ThomasDuvinage/UTBM_TZ20/hardware/electronic/electronic_schematic.sch

## EAGLE design hardware/electronic/electronic_schematic.sch (2020-06-02)

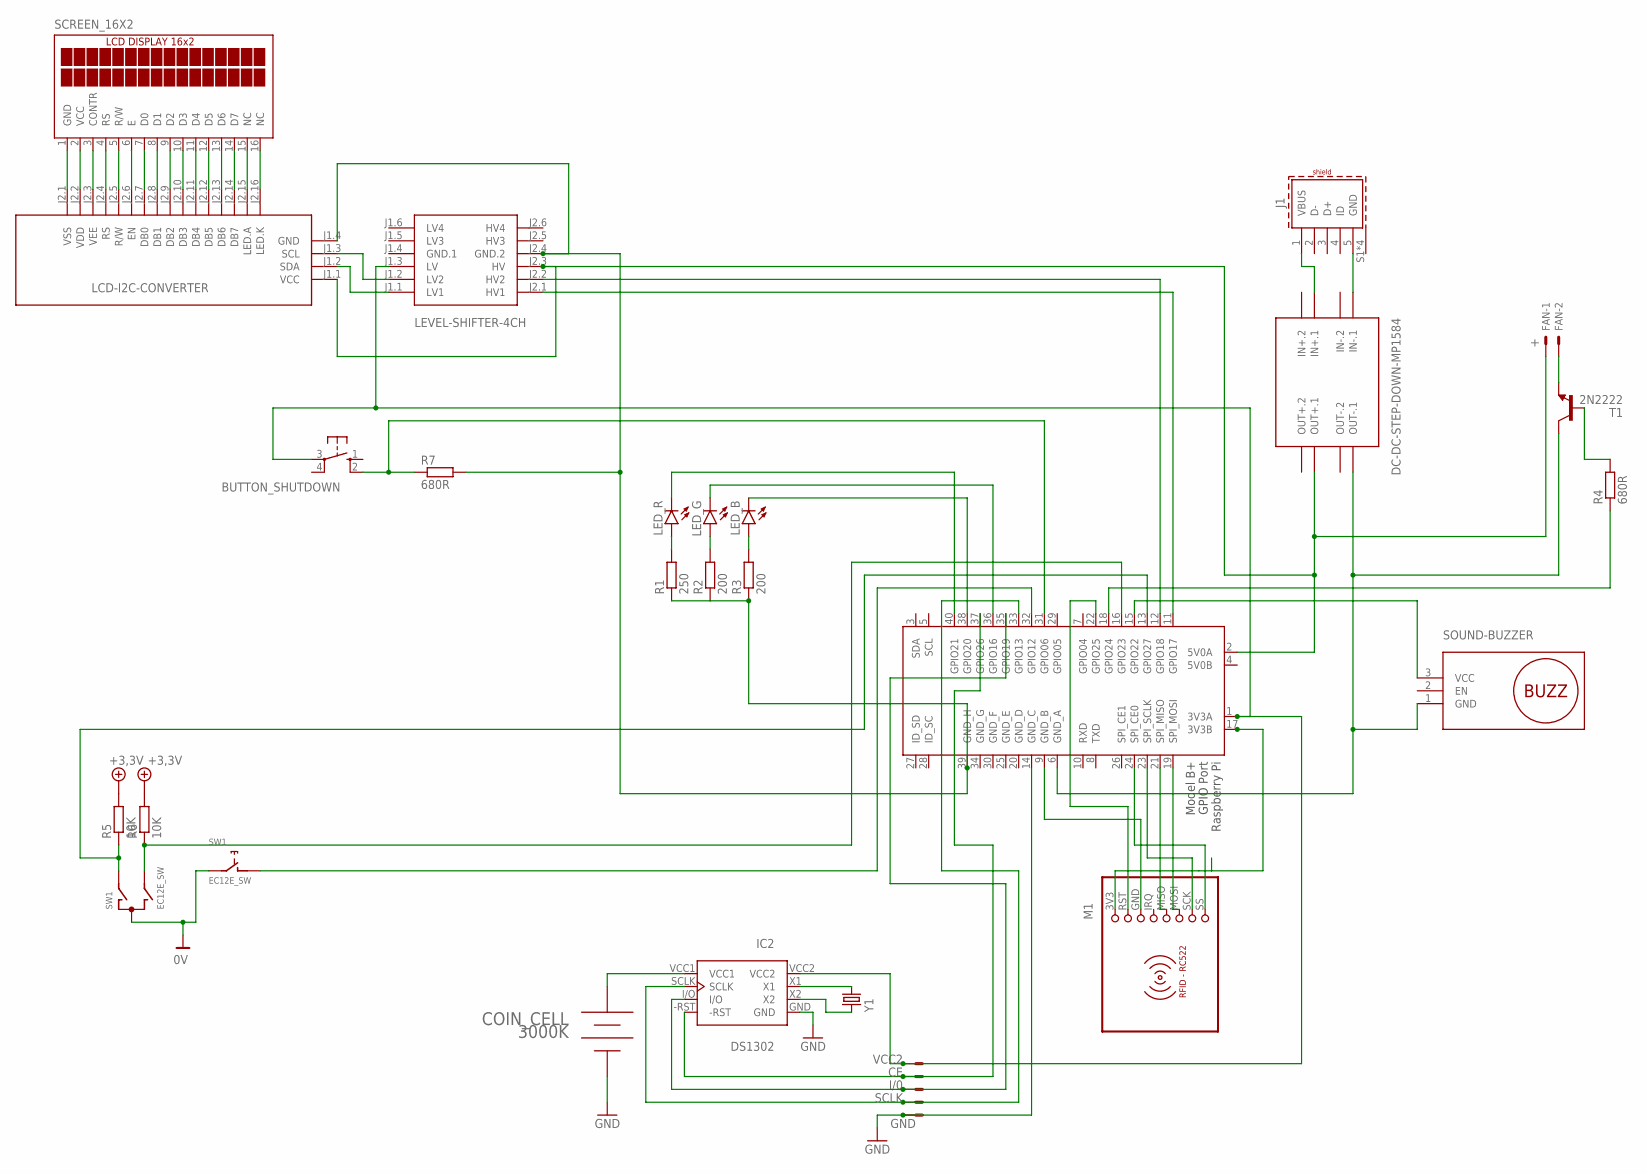
[picture p30: schematic electronic_schematic.sch]

Parts:
BUTTON_SHUTDOWN: 10-XX; B3F-10XX
COIN_CELL: 3000K
FAN: +; 22-23-2021
IC2: DS1302; DIL08
J1: 629105136821
LED_B: LED3MM
LED_G: LED3MM
LED_R: LED3MM
M1: RFID-RC522
R1: 250; 0207/10
R2, R3: 200; 0207/10
R4, R7: 680R; 0207/10
R5, R6: 10K; 0207/10
RTC: 22-23-2051
SCREEN_16X2: TUXGR_16X2_R2
SW1: EC12E_SW; ALPS_EC12E_SW
T1: 2N2222; TO18
U$1: LCD-I2C-CONVERTER
U$2: LEVEL-SHIFTER-4CH
U$4: SOUND-BUZZER
U$5: DC-DC-STEP-DOWN-MP1584
X1: RASPI_GPIO_B+#_BOX; RASPI_GPIO_B+_BOX
Y1: CC1V

Connections:
5+: FAN.1, U$1.J1.1 (VCC), U$2.J2.3 (HV), U$5.OUT+.1, X1.2 (5V0A)
+5V: R5.2, R6.2
-: COIN_CELL.-
CE: IC2.-RST, RTC.4, X1.37 (GPIO26)
GND: IC2.GND, RTC.1, SW1.C, SW1.E (2), X1.14 (GND_C)
I/0: IC2.I/O, RTC.3, X1.35 (GPIO19)
unnamed: LED_R.A, R1.2
unnamed: LED_G.A, R2.2
unnamed: LED_B.A, R3.2
unnamed: J1.5 (GND), U$5.IN-.1
unnamed: J1.1 (VBUS), U$5.IN+.1
unnamed: M1.SS (8), X1.24 (SPI_CE0)
unnamed: T1.3 (C), U$4.1 (GND), U$5.OUT-.1, X1.6 (GND_A)
unnamed: U$2.J2.1 (HV1), X1.11 (GPIO17)
unnamed: LED_R.K (C), X1.40 (GPIO21)
unnamed: LED_G.K (C), X1.36 (GPIO16)
unnamed: LED_B.K (C), X1.38 (GPIO20)
unnamed: SCREEN_16X2.1 (GND), U$1.J2.1 (VSS)
unnamed: SCREEN_16X2.2 (VCC), U$1.J2.2 (VDD)
unnamed: SCREEN_16X2.3 (CONTR), U$1.J2.3 (VEE)
unnamed: SCREEN_16X2.4 (RS), U$1.J2.4 (RS)
unnamed: SCREEN_16X2.5 (R/W), U$1.J2.5 (R/W)
unnamed: SCREEN_16X2.6 (E), U$1.J2.6 (EN)
unnamed: SCREEN_16X2.7 (D0), U$1.J2.7 (DB0)
unnamed: SCREEN_16X2.8 (D1), U$1.J2.8 (DB1)
unnamed: SCREEN_16X2.9 (D2), U$1.J2.9 (DB2)
unnamed: SCREEN_16X2.10 (D3), U$1.J2.10 (DB3)
unnamed: SCREEN_16X2.11 (D4), U$1.J2.11 (DB4)
unnamed: SCREEN_16X2.12 (D5), U$1.J2.12 (DB5)
unnamed: SCREEN_16X2.13 (D6), U$1.J2.13 (DB6)
unnamed: SCREEN_16X2.14 (D7), U$1.J2.14 (DB7)
unnamed: SCREEN_16X2.15 (NC), U$1.J2.15 (LED.A)
unnamed: SCREEN_16X2.16 (NC), U$1.J2.16 (LED.K)
unnamed: R1.1, R2.1, R3.1, R7.2, U$1.J1.4 (GND), U$2.J2.4 (GND.2), X1.39 (GND_H)
unnamed: BUTTON_SHUTDOWN.2 (S1), R7.1, X1.31 (GPIO06)
unnamed: U$1.J1.2 (SDA), U$2.J1.1 (LV1)
unnamed: U$1.J1.3 (SCL), U$2.J1.2 (LV2)
unnamed: U$2.J2.2 (HV2), X1.12 (GPIO18)
unnamed: R5.1, SW1.A, X1.13 (GPIO27)
unnamed: R6.1, SW1.B, X1.16 (GPIO23)
unnamed: SW1.D (1), X1.32 (GPIO12)
unnamed: U$4.3 (VCC), X1.15 (GPIO22)
unnamed: M1.MISO (5), X1.21 (SPI_MISO)
unnamed: M1.MOSI (6), X1.19 (SPI_MOSI)
unnamed: M1.SCK (7), X1.23 (SPI_SCLK)
unnamed: M1.3V3 (1), X1.17 (3V3B)
unnamed: M1.RST (2), X1.22 (GPIO25)
unnamed: M1.GND (3), X1.9 (GND_B)
unnamed: FAN.2, T1.1 (E)
unnamed: R4.2, T1.2 (B)
unnamed: R4.1, X1.18 (GPIO24)
unnamed: IC2.X1, Y1.'2' (2)
unnamed: IC2.X2, Y1.'1' (1)
SCLK: IC2.SCLK, RTC.2, X1.33 (GPIO13)
VCC1: COIN_CELL.+, IC2.VCC1
VCC2: BUTTON_SHUTDOWN.3, IC2.VCC2, RTC.5, U$2.J1.3 (LV), X1.1 (3V3A)
